circuitvalley/USB_C_Industrial_Camera_FPGA_USB3/Hardware/01_Camera_Sensors/IMX290_IMX327_IMX462/IMX290_module_sch.png

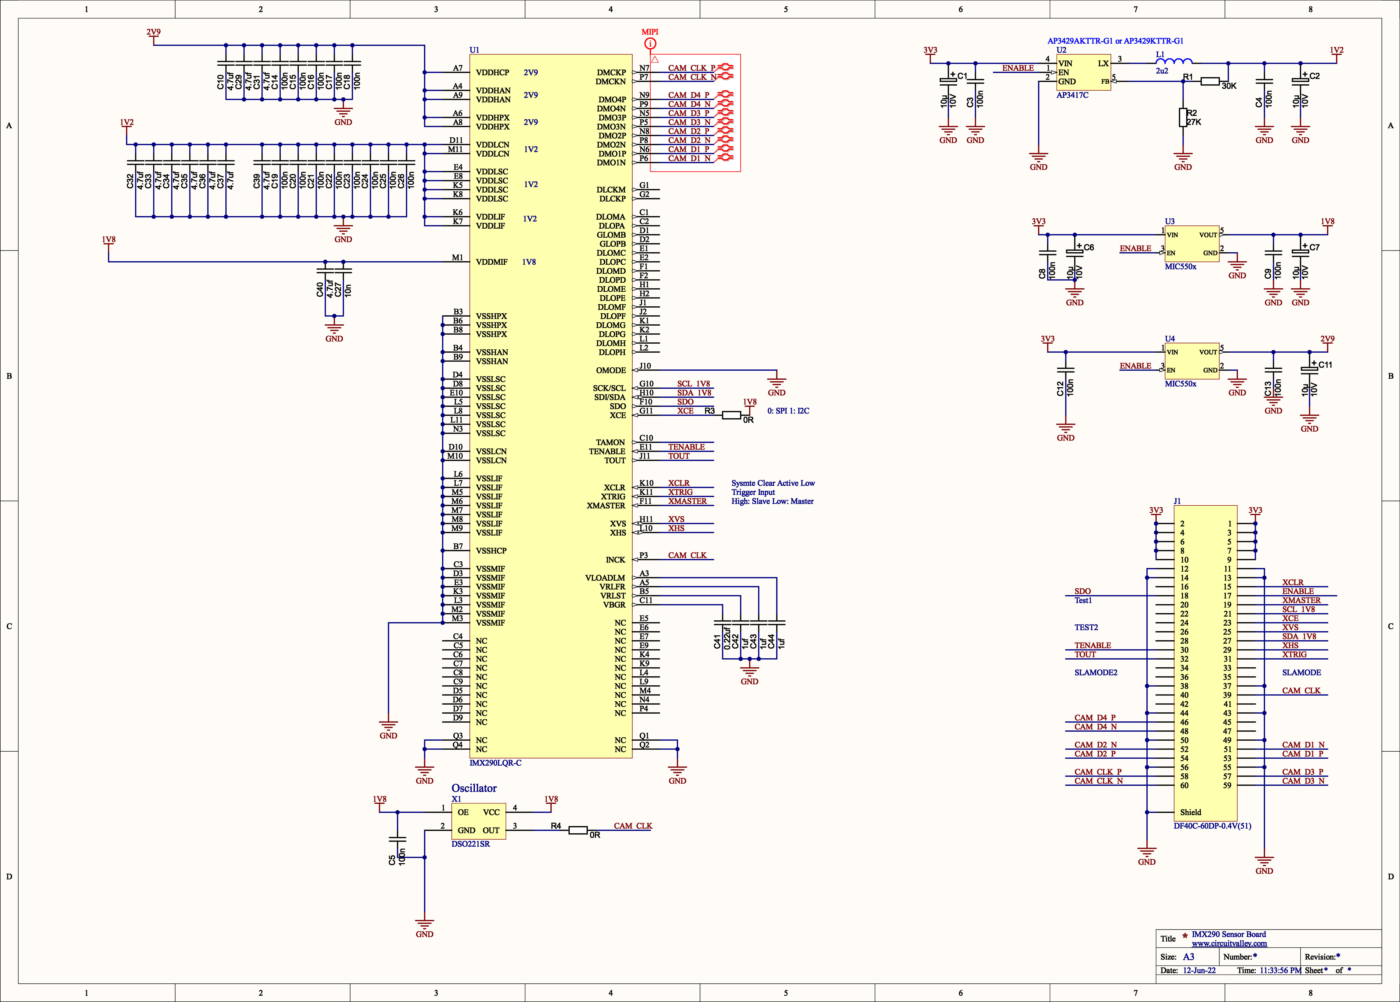
Hardware/01_Camera_Sensors/IMX290_IMX327_IMX462/IMX290_module_sch.png
