circuitvalley/USB_C_Industrial_Camera_FPGA_USB3/Hardware/01_Camera_Sensors/IMX477/IMX477_PCB.jpg

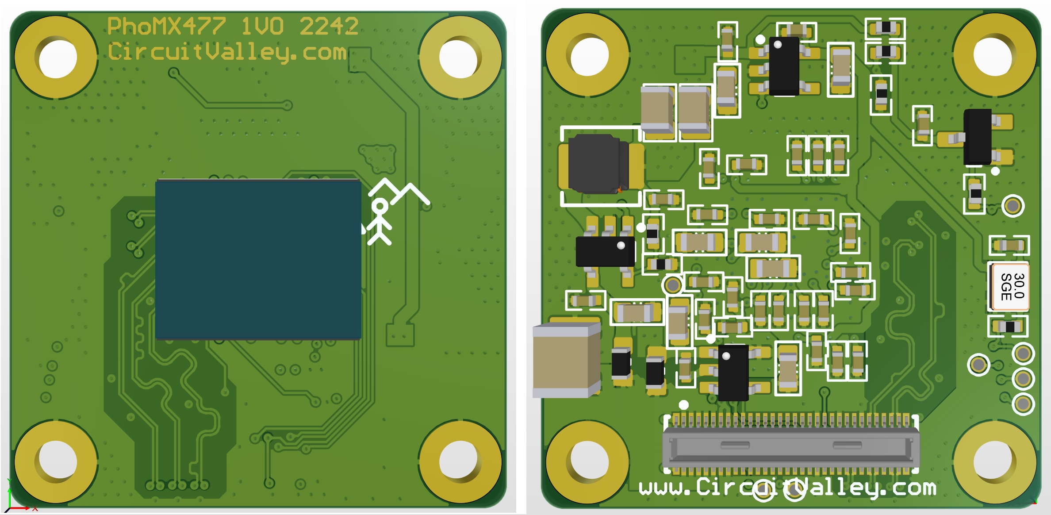
Hardware/01_Camera_Sensors/IMX477/IMX477_PCB.jpg
