circuitvalley/USB_C_Industrial_Camera_FPGA_USB3/Hardware/02_FPGA_Core/FPGA_Core_GPIF.png

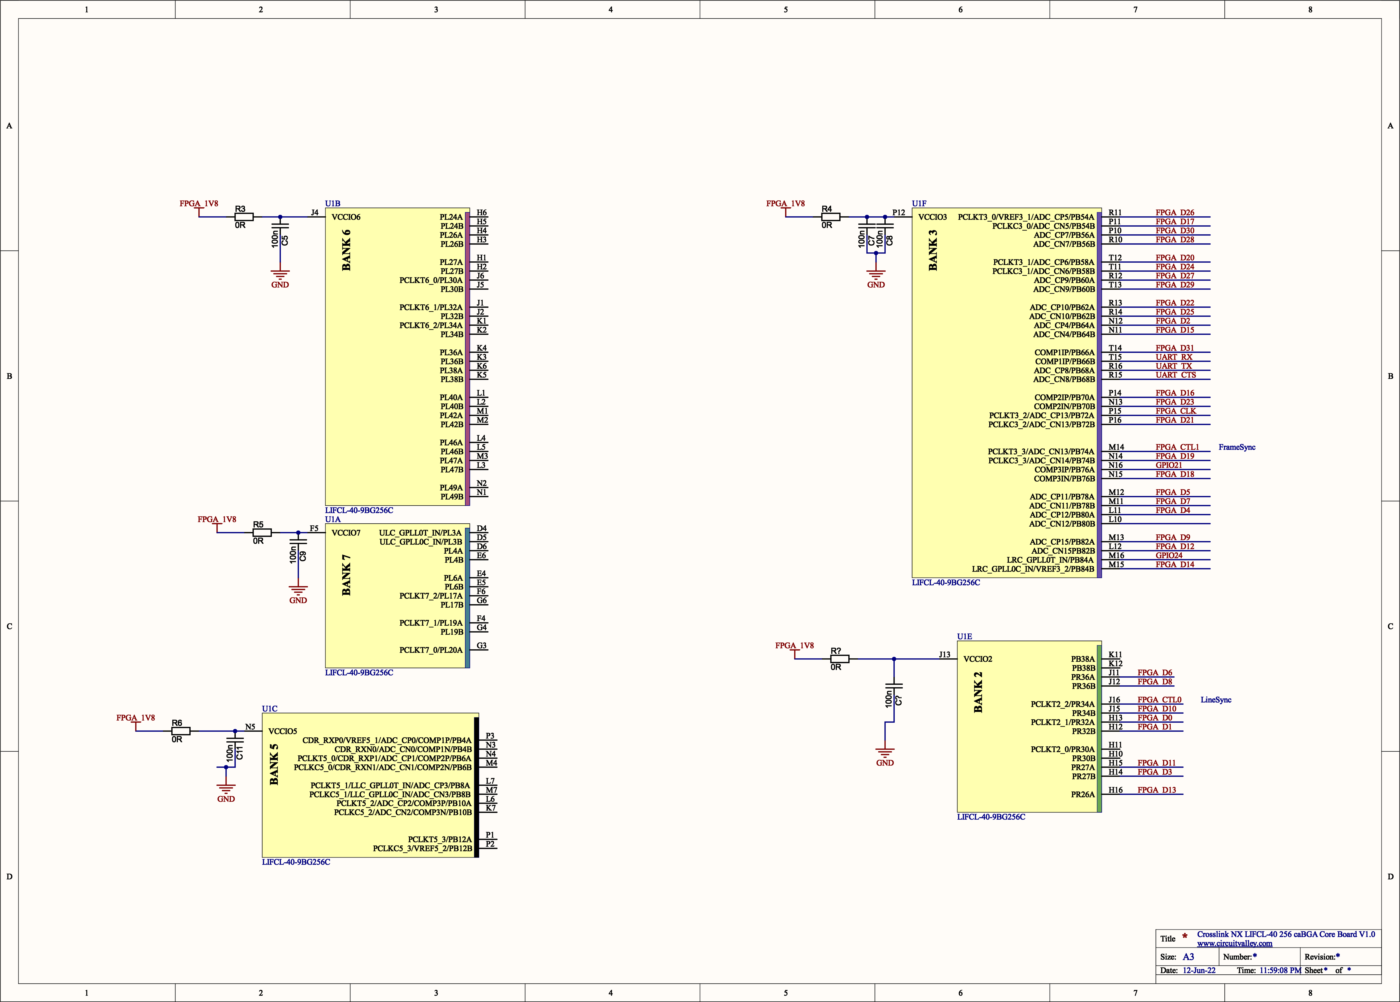
Hardware/02_FPGA_Core/FPGA_Core_GPIF.png
