circuitvalley/USB_C_Industrial_Camera_FPGA_USB3/Hardware/03_USB_Controller/USB_Controller_Schematic_usb.png

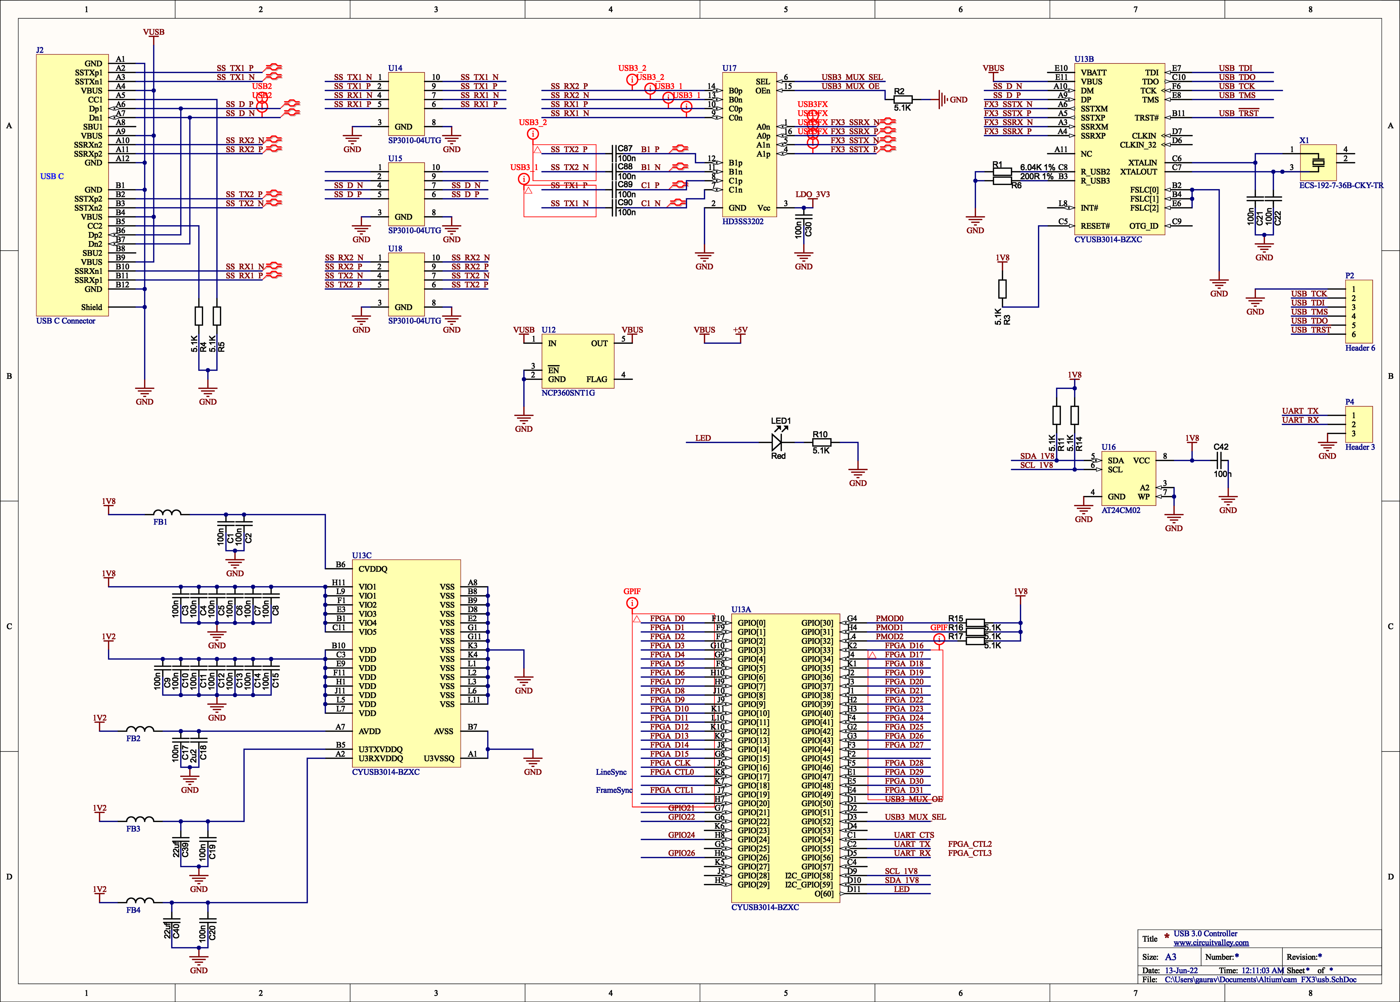
Hardware/03_USB_Controller/USB_Controller_Schematic_usb.png
