circuitvalley/USB_C_Industrial_Camera_FPGA_USB3/Hardware/Images/FPGA_core_lattice_crosslink_nx_pcb.png

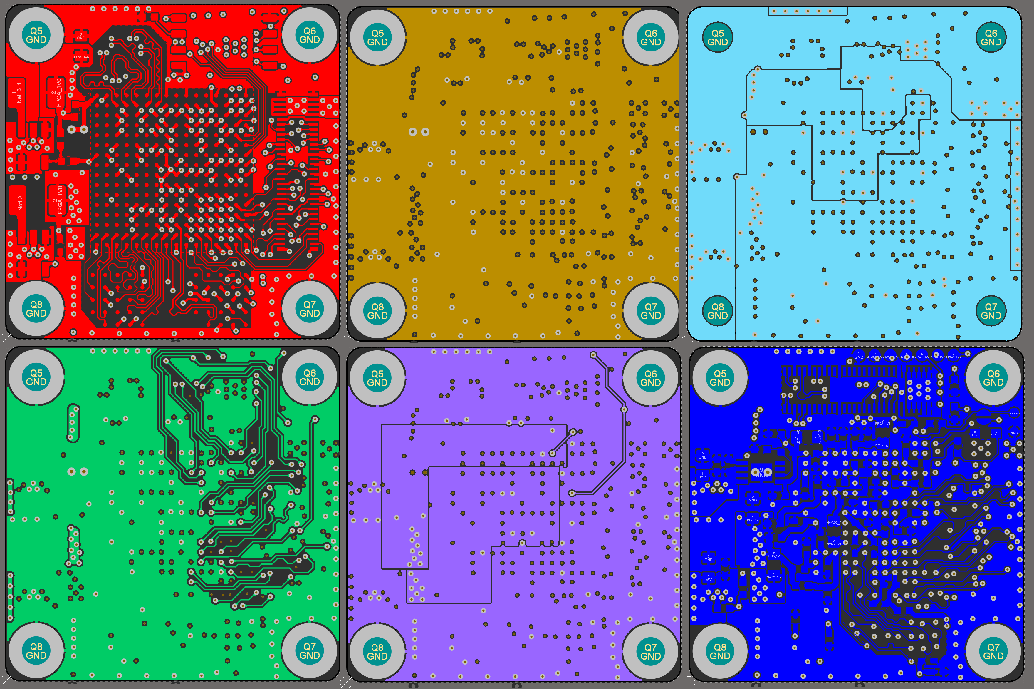
Hardware/Images/FPGA_core_lattice_crosslink_nx_pcb.png
