circuitvalley/USB_C_Industrial_Camera_FPGA_USB3/Hardware/Images/imx477.jpg

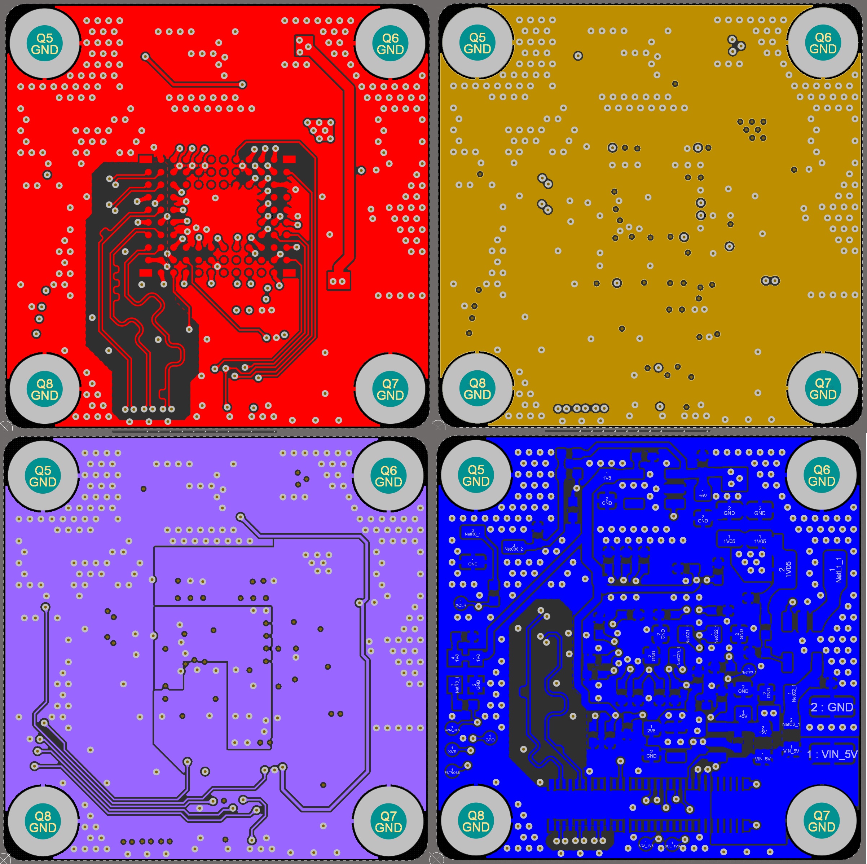
Hardware/Images/imx477.jpg
