circuitvalley/USB_C_Industrial_Camera_FPGA_USB3/Hardware/Images/usb_c_fpga_mipi_camera_c_mount_industrial_lattice_crosslink_fpga_xilinx_zynq (29).JPG

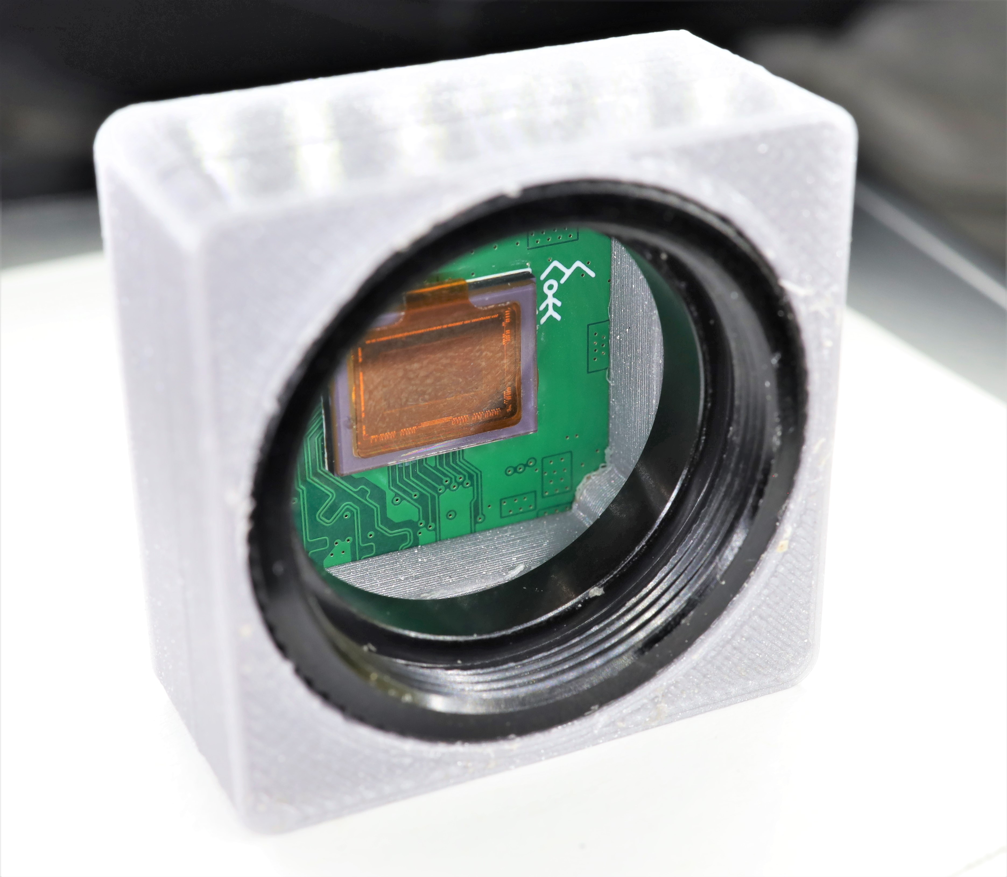
Hardware/Images/usb_c_fpga_mipi_camera_c_mount_industrial_lattice_crosslink_fpga_xilinx_zynq (29).JPG
