circuitvalley/USB_C_Industrial_Camera_FPGA_USB3/Hardware/Encolosure_Camera_mount/Lens_mount/3d_printed_lens_mont_c_mount.png

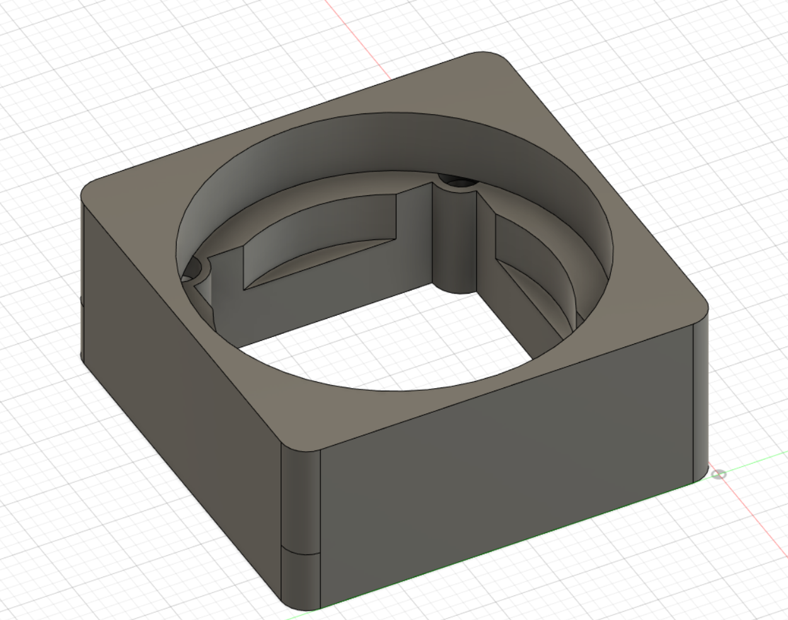
Hardware/Encolosure_Camera_mount/Lens_mount/3d_printed_lens_mont_c_mount.png
