circuitvalley/USB_C_Industrial_Camera_FPGA_USB3/FPGA_Firmware/Source/src/mipi_csi_rx_raw_depacker_8b2lane.v

`timescale 1ns/1ns

/*
MIPI CSI RX to Parallel Bridge (c) by Gaurav Singh www.CircuitValley.com

MIPI CSI RX to Parallel Bridge is licensed under a
Creative Commons Attribution 3.0 Unported License.

You should have received a copy of the license along with this
work.  If not, see <http://creativecommons.org/licenses/by/3.0/>.
*/

/*
Receives 4 lane raw mipi bytes from packet decoder, rearrange bytes to output 8 pixel 16bit each 
output is one clock cycle delayed, because the way , MIPI RAW is packed 
output come in chunk on each clock cycle, output_valid_o remains active only while 20 pixel chunk is outputted 
*/

module mipi_csi_rx_raw_depacker_8b2lane #(parameter PIXEL_WIDTH=16)(clk_i,
										data_valid_i,
										data_i,
										packet_type_i,
										raw_line_o,
										output_valid_o,
										output_o);
localparam [7:0]MIPI_GEAR = 8;
localparam [3:0]LANES = 3'h2;
localparam [3:0]PIXEL_PER_CLK = 4;

localparam [7:0]MIPI_CSI_PACKET_10bRAW = 8'h2B;
localparam [7:0]MIPI_CSI_PACKET_12bRAW = 8'h2C;
localparam [7:0]MIPI_CSI_PACKET_14bRAW = 8'h2D;

input clk_i;
input data_valid_i;
input [((MIPI_GEAR * LANES) - 1'h1) : 0]data_i;
input [2:0]packet_type_i;

output reg output_valid_o;
output reg [((PIXEL_WIDTH * PIXEL_PER_CLK) - 1) :0]output_o;
output raw_line_o;

reg [6:0]index_table_pixel_0[1:0];
reg [6:0]index_table_pixel_1[1:0];
reg [6:0]index_table_pixel_2[1:0];
reg [6:0]index_table_pixel_3[1:0];
reg [6:0]index_table_pixel_lsb1[1:0];


reg [6:0]index_table12_pixel_0[1:0];
reg [6:0]index_table12_pixel_1[1:0];
reg [6:0]index_table12_pixel_2[1:0];
reg [6:0]index_table12_pixel_3[1:0];
reg [6:0]index_table12_pixel_lsb1[1:0];

reg [6:0]index_table14_pixel_0[1:0];
reg [6:0]index_table14_pixel_1[1:0];
reg [6:0]index_table14_pixel_2[1:0];
reg [6:0]index_table14_pixel_3[1:0];
reg [6:0]index_table14_pixel_lsb1[1:0];


reg [6:0]offset_pixel_0;
reg [6:0]offset_pixel_1;
reg [6:0]offset_pixel_2;
reg [6:0]offset_pixel_3;
reg [6:0]offset_pixel_lsb1;

reg [6:0]offset12_pixel_0;
reg [6:0]offset12_pixel_1;
reg [6:0]offset12_pixel_2;
reg [6:0]offset12_pixel_3;
reg [6:0]offset12_pixel_lsb1;

reg [6:0]offset14_pixel_0;
reg [6:0]offset14_pixel_1;
reg [6:0]offset14_pixel_2;
reg [6:0]offset14_pixel_3;
reg [6:0]offset14_pixel_lsb1;

reg offset_index;

reg [((MIPI_GEAR * LANES) - 1'h1):0]last_data_i[5:0];
reg [2:0]byte_count;
reg [2:0]idle_count;

reg data_valid_reg;
reg [((MIPI_GEAR * LANES) - 1'h1):0]data_reg;
reg [2:0]burst_length_reg;
reg [2:0]idle_length_reg;
reg [2:0]packet_type_reg;

wire [2:0]burst_length;
wire [2:0]idle_length;
wire [((MIPI_GEAR * LANES * 5) - 1'h1) : 0]pipe10; 
wire [((MIPI_GEAR * LANES * 4) - 1'h1) : 0]pipe12;
wire [((MIPI_GEAR * LANES * 7) - 1'h1) : 0]pipe14;


reg [((PIXEL_WIDTH * PIXEL_PER_CLK) - 1'h1) :0]output_10b;
reg [((PIXEL_WIDTH * PIXEL_PER_CLK) - 1'h1) :0]output_12b;
reg [((PIXEL_WIDTH * PIXEL_PER_CLK) - 1'h1) :0]output_14b;
reg output_valid_reg;
reg output_valid_reg_2;

assign pipe10 = {data_reg , last_data_i[0], last_data_i[1], last_data_i[2], last_data_i[3]}; 

assign pipe12 = {data_reg , last_data_i[0], last_data_i[1], last_data_i[2]}; //would need last bytes as well as current data to get full 8 pixel , with 16x gering bytes are arrange as [bb,aa]

assign pipe14 = {data_reg , last_data_i[0], last_data_i[1], last_data_i[2], last_data_i[3], last_data_i[4], last_data_i[5]}; 


assign burst_length =  (packet_type_i == (MIPI_CSI_PACKET_12bRAW & 8'h07))? 3'd2:3'd3;  //active + 1

assign idle_length =  (packet_type_i == (MIPI_CSI_PACKET_10bRAW & 8'h07))? 3'd3: ((packet_type_i == (MIPI_CSI_PACKET_12bRAW & 8'h07))? 3'd2 : 3'd5); //inactive


assign raw_line_o = data_valid_i| output_valid_reg | output_valid_reg_2 | output_valid_o;

always @(*)
begin
    output_10b[(PIXEL_WIDTH * 3)   +: PIXEL_WIDTH] =    {pipe10 [offset_pixel_3   +:8],   pipe10[(offset_pixel_lsb1 + 6)    +:2],  {(PIXEL_WIDTH - 10){1'b0}}};             //lane 2 //add ( PIXEL_WIDTH - 10 ) padding in the LSbits
    output_10b[(PIXEL_WIDTH * 2)   +: PIXEL_WIDTH] =    {pipe10 [offset_pixel_2   +:8],   pipe10[(offset_pixel_lsb1 + 4)    +:2],  {(PIXEL_WIDTH - 10){1'b0}}};             //lane 2 //add ( PIXEL_WIDTH - 10 ) padding in the LSbits
    output_10b[(PIXEL_WIDTH)       +: PIXEL_WIDTH] =    {pipe10 [offset_pixel_1   +:8],   pipe10[(offset_pixel_lsb1 + 2)    +:2],  {(PIXEL_WIDTH - 10){1'b0}}};             //lane 2 //add ( PIXEL_WIDTH - 10 ) padding in the LSbits
    output_10b[0                   +: PIXEL_WIDTH] =    {pipe10 [offset_pixel_0   +:8],   pipe10[ offset_pixel_lsb1    		+:2],  {(PIXEL_WIDTH - 10){1'b0}}};             //lane 1 first pixel on wire
        //RAW10 additional LSbits  are as follow [ pixel3 pixel2 pixel 1 pixel0]

    output_12b[(PIXEL_WIDTH * 3)   +: PIXEL_WIDTH] =    {pipe12 [offset12_pixel_3 +:8],   pipe12[(offset12_pixel_lsb1 + 28) +:4],  {(PIXEL_WIDTH - 12){1'b0}}};
    output_12b[(PIXEL_WIDTH * 2)   +: PIXEL_WIDTH] =    {pipe12 [offset12_pixel_2 +:8],   pipe12[(offset12_pixel_lsb1 + 24) +:4],  {(PIXEL_WIDTH - 12){1'b0}}};
    output_12b[(PIXEL_WIDTH)       +: PIXEL_WIDTH] =    {pipe12 [offset12_pixel_1 +:8],   pipe12[(offset12_pixel_lsb1 + 4)  +:4],  {(PIXEL_WIDTH - 12){1'b0}}};
    output_12b[0                   +: PIXEL_WIDTH] =    {pipe12 [offset12_pixel_0 +:8],   pipe12[ offset12_pixel_lsb1  		+:4],  {(PIXEL_WIDTH - 12){1'b0}}};             //lane 1 first pixel on wire
        //RAW12 additional LSbits  are as follow [pixel 1 pixel0]

    //output_14b[(PIXEL_WIDTH * 3)   +: PIXEL_WIDTH] =    {pipe14 [offset14_pixel_3 +:8],   pipe14[offset14_pixel_lsb1  + 18) +:6],  {(PIXEL_WIDTH - 14){1'b0}}};
    //output_14b[(PIXEL_WIDTH * 2)   +: PIXEL_WIDTH] =    {pipe14 [offset14_pixel_2 +:8],   pipe14[(offset14_pixel_lsb1 + 12) +:6],  {(PIXEL_WIDTH - 14){1'b0}}};
    //output_14b[(PIXEL_WIDTH)       +: PIXEL_WIDTH] =    {pipe14 [offset14_pixel_1 +:8],   pipe14[(offset14_pixel_lsb1 + 6)  +:6],  {(PIXEL_WIDTH - 14){1'b0}}};
    //output_14b[0                   +: PIXEL_WIDTH] =    {pipe14 [offset14_pixel_0 +:8],   pipe14[ offset14_pixel_lsb1		  +:6],  {(PIXEL_WIDTH - 14){1'b0}}};             //lane 1 first pixel on wire

end

always @(posedge clk_i)
begin


        if (packet_type_reg == (MIPI_CSI_PACKET_10bRAW & 8'h07))
        begin
                output_o <= output_10b;
        end
        else if (packet_type_reg == (MIPI_CSI_PACKET_12bRAW & 8'h07))
        begin
                output_o <= output_12b;
        end
        else // if (packet_type_i == (MIPI_CSI_PACKET_14bRAW & 8'h07))
        begin
                output_o <= output_14b;
        end

end



always @(posedge clk_i)
begin

                output_valid_reg_2 <= output_valid_reg;
                output_valid_o <= output_valid_reg_2;

                if (output_valid_reg_2)
                begin
                        offset_index = !offset_index ;
                end
                else
                begin
                        offset_index = 0;
                end

                offset_pixel_0 <= index_table_pixel_0[offset_index];
                offset_pixel_1 <= index_table_pixel_1[offset_index];
                offset_pixel_2 <= index_table_pixel_2[offset_index];
                offset_pixel_3 <= index_table_pixel_3[offset_index];
                offset_pixel_lsb1 <= index_table_pixel_lsb1[offset_index];

                offset12_pixel_0 <= index_table12_pixel_0[offset_index];
                offset12_pixel_1 <= index_table12_pixel_1[offset_index];
				offset12_pixel_2 <= index_table12_pixel_2[offset_index];
				offset12_pixel_3 <= index_table12_pixel_3[offset_index];
                offset12_pixel_lsb1 <= index_table12_pixel_lsb1[offset_index];


                offset14_pixel_0 <= index_table14_pixel_0[offset_index];
                offset14_pixel_1 <= index_table14_pixel_1[offset_index];
				offset14_pixel_2 <= index_table14_pixel_2[offset_index];
				offset14_pixel_3 <= index_table14_pixel_3[offset_index];
                offset14_pixel_lsb1 <= index_table14_pixel_lsb1[offset_index];
end

always @(posedge clk_i )//or negedge data_valid_reg)
begin

        if (data_valid_reg)
        begin

                if (byte_count < (burst_length_reg))
                begin
                        byte_count <= byte_count + 1'd1;
                        idle_count <= idle_length_reg - 1'b1;

                        output_valid_reg <= 1'b1;

                end
                else
                begin
                        idle_count <= idle_count - 1'b1;
                        if (!idle_count)
                        begin
                                byte_count <= 4'b1;             //set to 1 to enable output_valid_o with next edge
                        end

                        output_valid_reg <= 1'h0;
                end


        end
        else
        begin

                byte_count <= burst_length;

                index_table_pixel_0[0] <= 0;
                index_table_pixel_0[1] <= 24;

                index_table_pixel_1[0] <= 8;
                index_table_pixel_1[1] <= 32;

                index_table_pixel_2[0] <= 16;
                index_table_pixel_2[1] <= 40;

                index_table_pixel_3[0] <= 24;
                index_table_pixel_3[1] <= 48;

                index_table_pixel_lsb1[0] <= 32;
                index_table_pixel_lsb1[1] <= 56;

                index_table12_pixel_0[0] <= 0;  //only first index matter with 12bit
                index_table12_pixel_0[1] <= 0;

                index_table12_pixel_1[0] <= 8;
                index_table12_pixel_1[1] <= 0;

                index_table12_pixel_2[0] <= 24;
                index_table12_pixel_2[1] <= 0;

                index_table12_pixel_3[0] <= 32;
                index_table12_pixel_3[1] <= 0;

                index_table12_pixel_lsb1[0] <= 16;
                index_table12_pixel_lsb1[1] <= 0;

                index_table14_pixel_0[0] <= 0;
                index_table14_pixel_0[1] <= 40;

                index_table14_pixel_1[0] <= 8;
                index_table14_pixel_1[1] <= 48;

                index_table14_pixel_2[0] <= 16;
                index_table14_pixel_2[1] <= 56;

                index_table14_pixel_3[0] <= 24;
                index_table14_pixel_3[1] <= 64;

                index_table14_pixel_lsb1[0] <= 32;
                index_table14_pixel_lsb1[1] <= 72;


                if (packet_type_i == (MIPI_CSI_PACKET_14bRAW & 8'h07))          // for 14bit need to wait for 3 sample while 12bit and 10bit only need 1 sample delay
                begin
                        idle_count <= 3'd4;
                end
                else if (packet_type_i == (MIPI_CSI_PACKET_10bRAW & 8'h07))
				begin
						idle_count <= 3'b1; 
				end
				else				
                begin
                        idle_count <= 3'b0;     //need to be zero to wait for 1 sample after data become valid
                end

                output_valid_reg <= 1'h0;
                burst_length_reg <= burst_length;
                idle_length_reg <= idle_length;
                packet_type_reg <= packet_type_i;
        end
end

always @(posedge clk_i)
begin
                data_valid_reg <= data_valid_i;
                data_reg <= data_i;

                last_data_i[0] <= data_reg;
                last_data_i[1] <= last_data_i[0];
                last_data_i[2] <= last_data_i[1];
				last_data_i[2] <= last_data_i[1];
				last_data_i[3] <= last_data_i[2];
				last_data_i[4] <= last_data_i[3];
				last_data_i[5] <= last_data_i[4];

end

endmodule
