circuitvalley/USB_C_Industrial_Camera_FPGA_USB3/FPGA_Firmware/Source/Testblocks/tb_mipi_csi_rx_byte_aligner.v

`timescale 1ns/1ns

module tb_rx_byte_aligner;
	
	reg clk;
	reg reset;
	reg  [15:0]byte_i;
	wire [15:0]byte_o;

GSR 
GSR_INST (
	.GSR_N(1'b1),
	.CLK(1'b0)
);

wire byte_synced;
mipi_csi_rx_byte_aligner byte_inst1(	.clk_i(clk),
									.reset_i(reset),
									.byte_i(byte_i),
									.byte_o(byte_o[15:0]),
									.byte_valid_o(byte_synced));

						
task sendbyte;
	input [15:0]byte;
	begin
	byte_i = byte;
	clk = 1'b1;
	#4
	clk = 1'b0;
	#4;
	end
endtask

initial begin
		clk = 1'b1;
		reset = 1'b1;
		clk = 1'b1;
		#4
		clk = 1'b0;
		#4;
		#50
		reset = 1'b0;
		sendbyte(16'h00);
		sendbyte(16'h00);
		sendbyte(16'h00);
		sendbyte(16'h00);
		sendbyte(16'h00);
		sendbyte(16'h2577);  //B8 2B 11 72 16 11 83 11
		sendbyte(16'hCE42);
		sendbyte(16'h2222);
		sendbyte(16'h6222);
		sendbyte(16'h2230);
		sendbyte(16'h2202);
		sendbyte(16'h2202);
		sendbyte(16'h2222);
		sendbyte(16'h2230);
		sendbyte(16'h2202);
		sendbyte(16'h2202);
		sendbyte(16'h2222);
		sendbyte(16'h2230);
		sendbyte(16'h2202);
		sendbyte(16'h2202);
		sendbyte(16'h2202);
		sendbyte(16'h2222);
		sendbyte(16'h2202);
		sendbyte(16'h2202);
		sendbyte(16'h2222);
		sendbyte(16'h2230);
		sendbyte(16'h2202);
		sendbyte(16'h2202);
		sendbyte(16'h2222);
		sendbyte(16'h2230);
		sendbyte(16'h2202);
		sendbyte(16'h2202);
		sendbyte(16'h2202);
		sendbyte(16'h2202);
		sendbyte(16'h2202);
		sendbyte(16'h2222);
		sendbyte(16'h2230);
		sendbyte(16'h2202);
		sendbyte(16'h2202);
		sendbyte(16'h2222);
		sendbyte(16'h2230);
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
		
		reset = 1'b0;
		sendbyte(16'h00);
		sendbyte(16'h00);
		sendbyte(16'h00);
		sendbyte(16'h00);
		sendbyte(16'h00);
		sendbyte(16'h82E0); 	//B8 60 11
		sendbyte(16'h4045);
		sendbyte(16'h45C4);
		sendbyte(16'h0840);
		sendbyte(16'h0817);
		sendbyte(16'h0808);
		reset = 1'h1;	
		
end

endmodule
